mug31/Split_MechanicalKeyboard_usingESP32DevMod/images/1763949235602.jpg

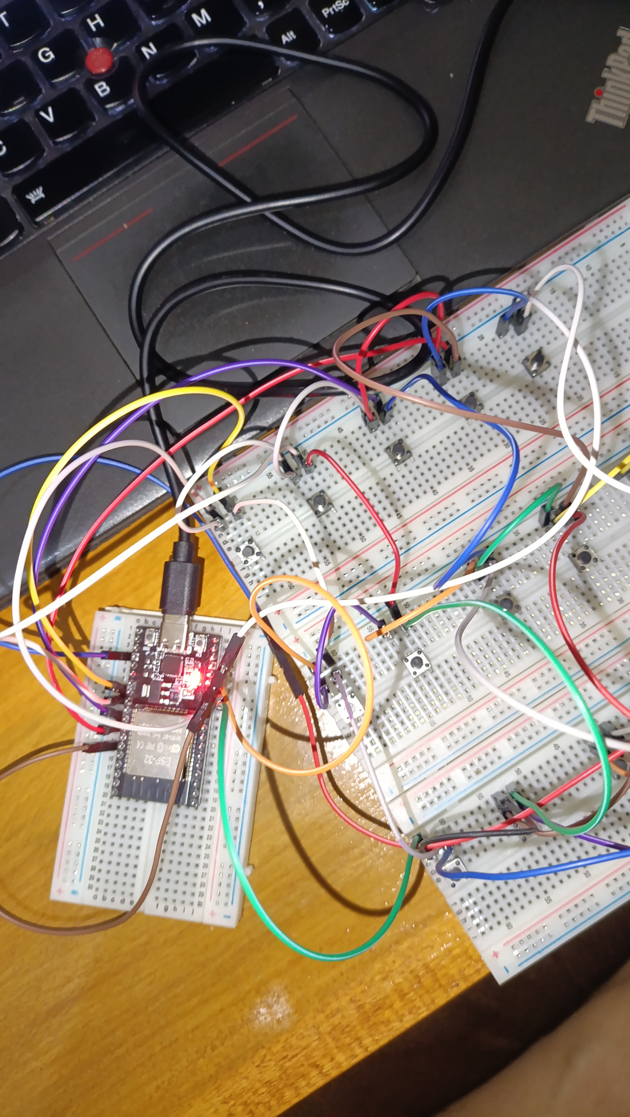
images/1763949235602.jpg
