mug31/Split_MechanicalKeyboard_usingESP32DevMod/images/1763949235726.jpg

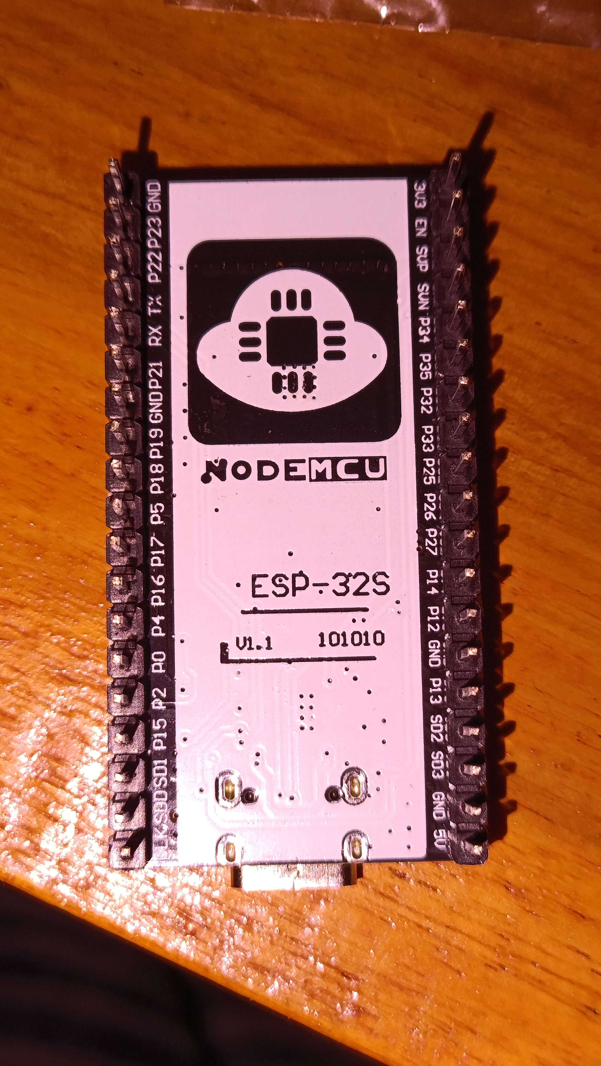
images/1763949235726.jpg
